darakuneko/Noraneko/noraneko42o/v1.0/firmware/noraneko42o/readme.md

# noraneko42o

noraneko42o

*A short description of the keyboard/project*

* Keyboard Maintainer: [Daraku-Neko](https://github.com/Daraku-Neko)
* Hardware Supported: *The PCBs, controllers supported*
* Hardware Availability: *Links to where you can find this hardware*

Make example for this keyboard (after setting up your build environment):

    make noraneko42o:default

See the [build environment setup](https://docs.qmk.fm/#/getting_started_build_tools) and the [make instructions](https://docs.qmk.fm/#/getting_started_make_guide) for more information. Brand new to QMK? Start with our [Complete Newbs Guide](https://docs.qmk.fm/#/newbs).

## Bootloader

Enter the bootloader in 3 ways:

* **Bootmagic reset**: Hold down the key at (0,0) in the matrix (usually the top left key or Escape) and plug in the keyboard
* **Physical reset button**: Briefly press the button on the back of the PCB - some may have pads you must short instead
* **Keycode in layout**: Press the key mapped to `QK_BOOT` if it is available
