darakuneko/Noraneko/noraneko52r/v1.1/plate/elecrow/noraneko52r-bottom-Thickness3mm.pdf

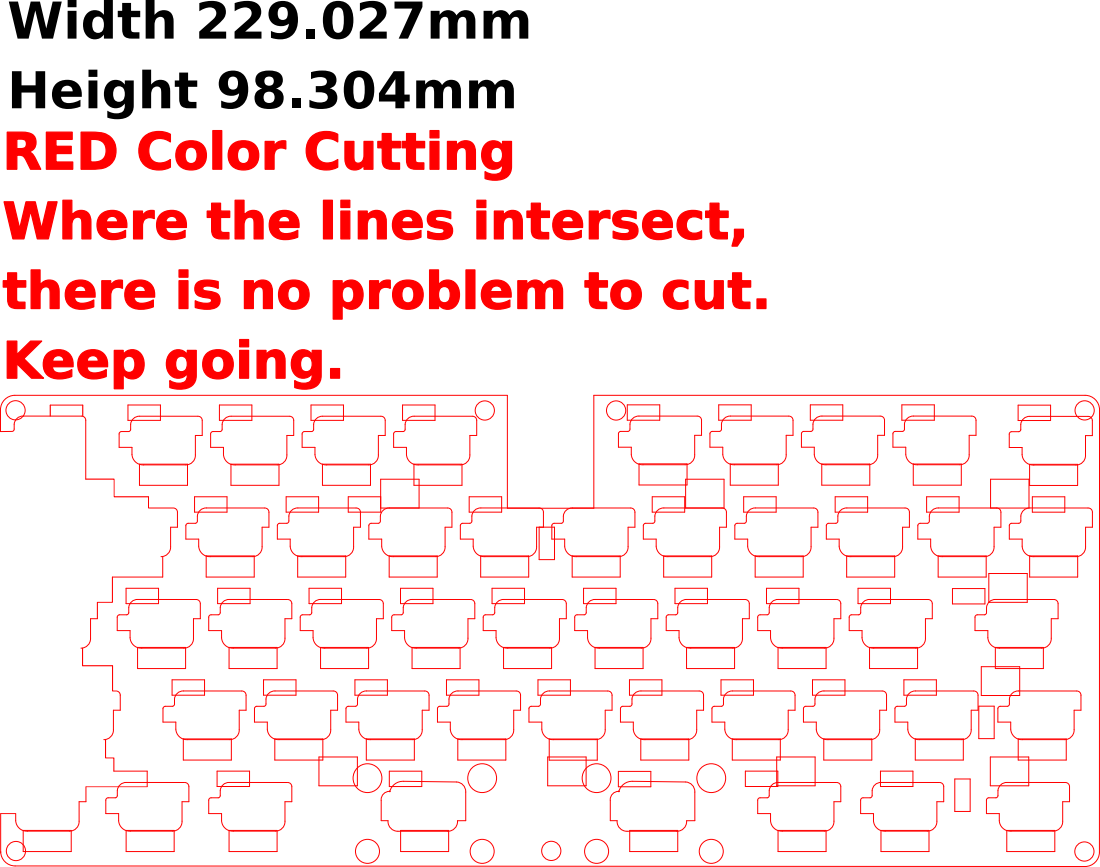
[picture p6: page 1]

Width 229.027mm
Height 98.304mm
RED Color Cutting
Where the lines intersect,
there is no problem to cut.
Keep going.
