darakuneko/Noraneko/noraneko52r/v1.1/plate/elecrow/noraneko52r-bottom-Thickness2mm.pdf

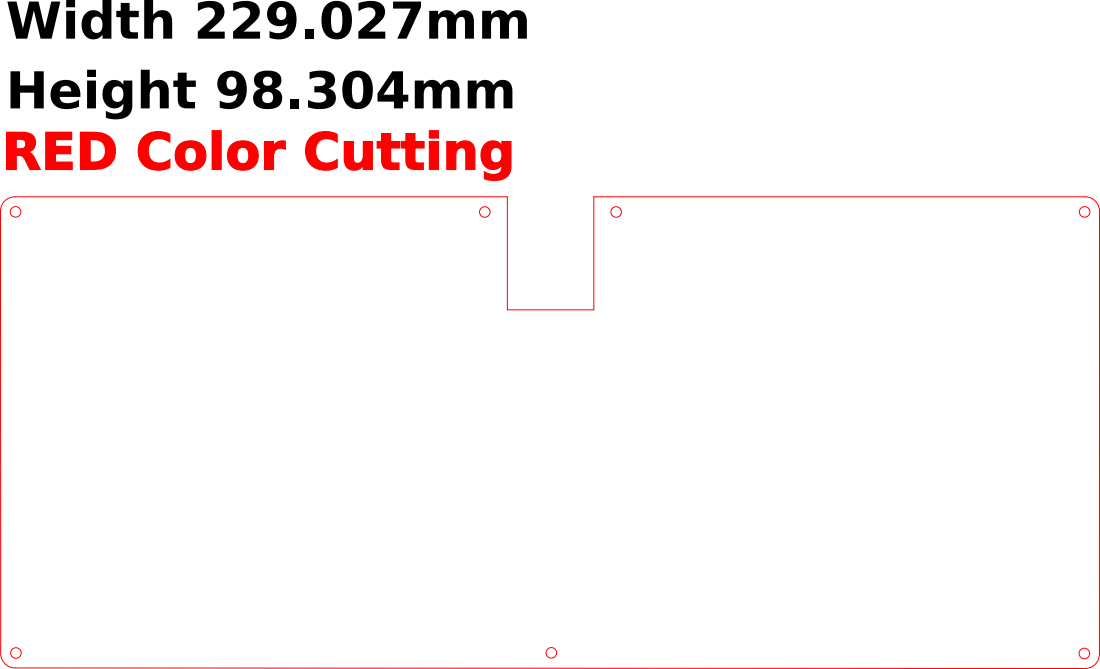
[picture p7: page 1]

Width 229.027mm
Height 98.304mm
RED Color Cutting
