darakuneko/Noraneko/noraneko52r/v1.1/plate/elecrow/noraneko52r-top-Thickness2mm.pdf

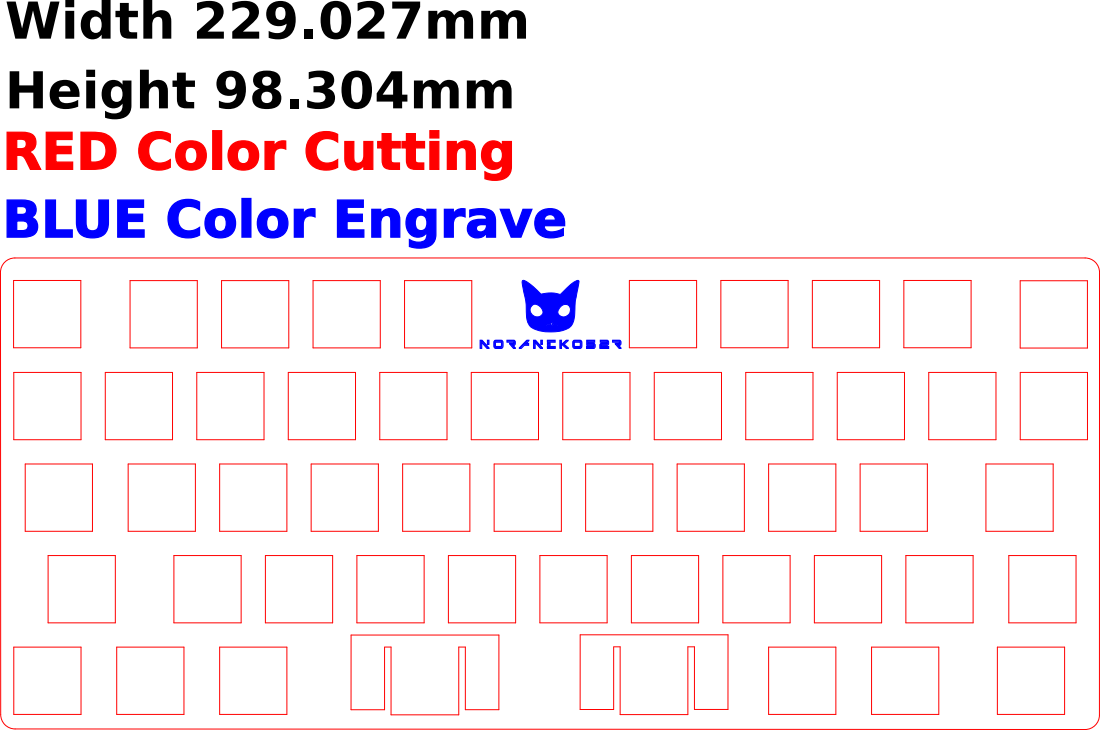
[picture p8: page 1]
Noraneko52R

Width 229.027mm
Height 98.304mm
RED Color Cutting
BLUE Color Engrave
