darakuneko/Noraneko/noraneko42c/v2.0/plate/elecrow/noraneko-top-Thickness3mm.pdf

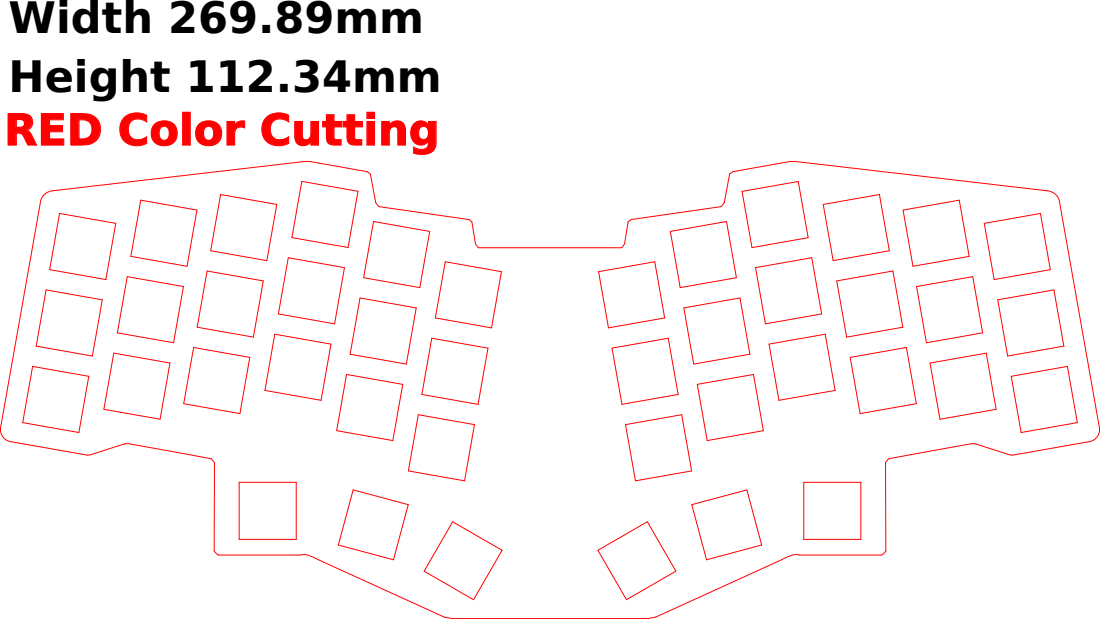
[picture p9: page 1]

Width 269.89mm
Height 112.34mm
RED Color Cutting
