darakuneko/Noraneko/noraneko52r/v1.0/plate/blackout/elecrow/blackout-noraneko52r-top-Thickness2mm.pdf

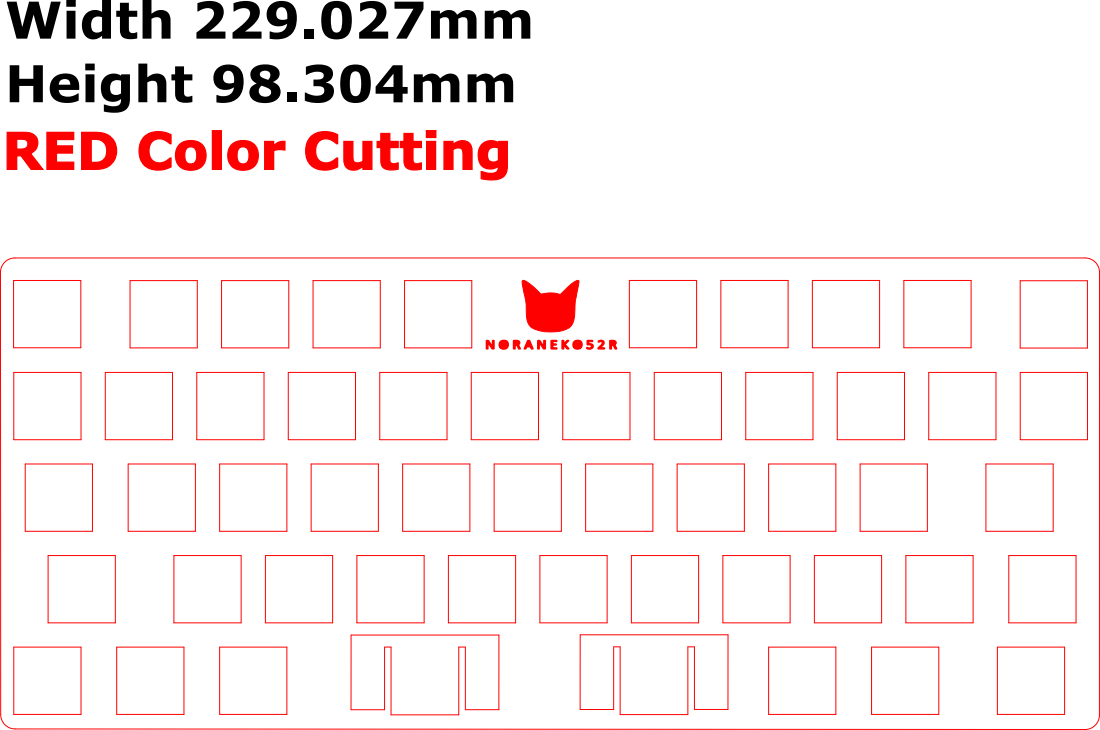
[picture p11: page 1]

Width 229.027mm
Height 98.304mm
RED Color Cutting
