darakuneko/Noraneko/noraneko52r/v1.1/pcb/noraneko52r.kicad_sch

## KiCad design noraneko52r/v1.1/pcb/noraneko52r.kicad_sch (2022-11-11)

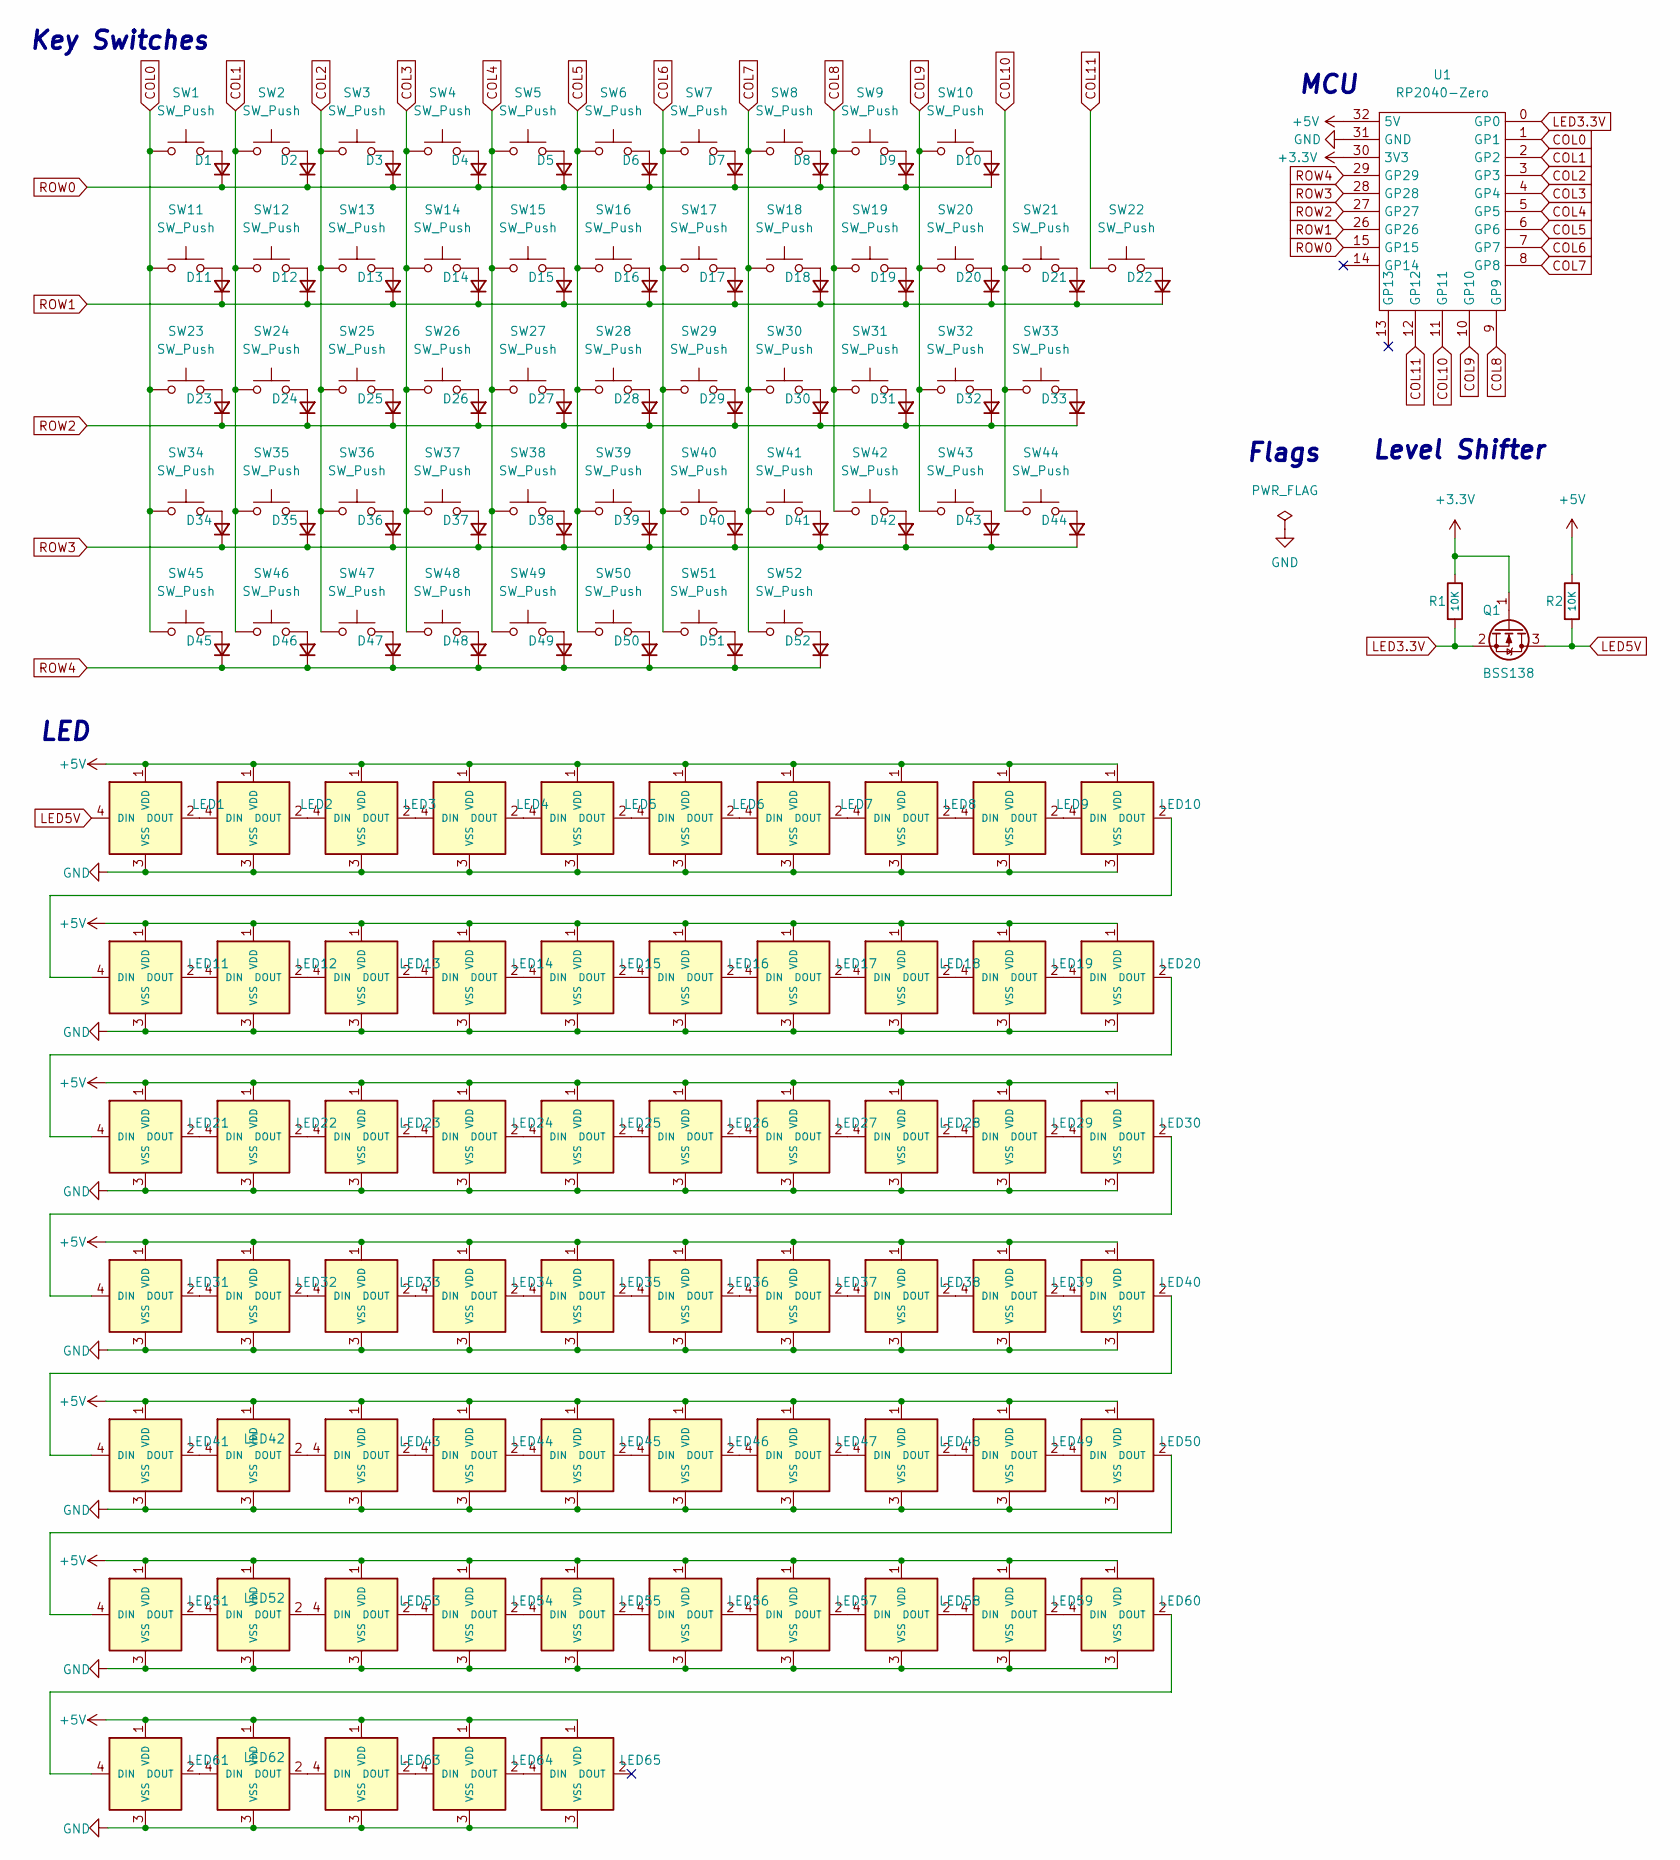
[picture p15: schematic noraneko52r.kicad_sch]

Parts:
D1, D2, D3, D4, D5, D6, D7, D8, D9, D10, D11, D12, D13, D14, D15, D16, D17, D18, D19, D20, D21, D22, D23, D24, D25, D26, D27, D28, D29, D30, D31, D32, D33, D34, D35, D36, D37, D38, D39, D40, D41, D42, D43, D44, D45, D46, D47, D48, D49, D50, D51, D52: D; 1N4148W; LCSC C81598
LED1, LED2, LED3, LED4, LED5, LED6, LED7, LED8, LED9, LED10, LED11, LED12, LED13, LED14, LED15, LED16, LED17, LED18, LED19, LED20, LED21, LED22, LED23, LED24, LED25, LED26, LED27, LED28, LED29, LED30, LED31, LED32, LED33, LED34, LED35, LED36, LED37, LED38, LED39, LED40, LED41, LED42, LED43, LED44, LED45, LED46, LED47, LED48, LED49, LED50, LED51, LED52: SK6812MINI-E
LED53, LED54, LED55, LED56, LED57, LED58, LED59, LED60, LED61, LED62, LED63, LED64, LED65: SK6812MINI-E; LED_WS2812B_PLCC4_5.0x5.0mm_P3.2mm; LCSC C2843785
Q1: BSS138; SOT-23; LCSC C2874697
R1, R2: 10K; R_Axial_DIN0207_L6.3mm_D2.5mm_P7.62mm_Horizontal
SW1, SW2, SW3, SW4, SW5, SW6, SW7, SW8, SW9, SW10, SW11, SW12, SW13, SW14, SW15, SW16, SW17, SW18, SW19, SW20, SW21, SW22, SW24, SW25, SW26, SW27, SW28, SW29, SW30, SW31, SW32, SW35, SW36, SW37, SW38, SW39, SW40, SW41, SW42, SW43, SW45, SW47, SW50: SW_Push; MX_Socket
SW23, SW44, SW46, SW51: SW_Push; MX_Socket_1.25U
SW33, SW34: SW_Push; MX_Socket_1.75U
SW48: SW_Push; MX_Socket_2.75U_Re
SW49: SW_Push; MX_Socket_2.25U_Re
SW52: SW_Push; MX_Socket_1.50U
U1: RP2040-Zero; RP2040-Zero-THT

Connections:
+3.3V: Q1.1 (G), R1.1, U1.30 (3V3)
+5V: LED1.1 (VDD), LED2.1 (VDD), LED3.1 (VDD), LED4.1 (VDD), LED5.1 (VDD), LED6.1 (VDD), LED7.1 (VDD), LED8.1 (VDD), LED9.1 (VDD), LED10.1 (VDD), LED11.1 (VDD), LED12.1 (VDD), LED13.1 (VDD), LED14.1 (VDD), LED15.1 (VDD), LED16.1 (VDD), LED17.1 (VDD), LED18.1 (VDD), LED19.1 (VDD), LED20.1 (VDD), LED21.1 (VDD), LED22.1 (VDD), LED23.1 (VDD), LED24.1 (VDD), LED25.1 (VDD), LED26.1 (VDD), LED27.1 (VDD), LED28.1 (VDD), LED29.1 (VDD), LED30.1 (VDD), LED31.1 (VDD), LED32.1 (VDD), LED33.1 (VDD), LED34.1 (VDD), LED35.1 (VDD), LED36.1 (VDD), LED37.1 (VDD), LED38.1 (VDD), LED39.1 (VDD), LED40.1 (VDD), LED41.1 (VDD), LED42.1 (VDD), LED43.1 (VDD), LED44.1 (VDD), LED45.1 (VDD), LED46.1 (VDD), LED47.1 (VDD), LED48.1 (VDD), LED49.1 (VDD), LED50.1 (VDD), LED51.1 (VDD), LED52.1 (VDD), LED53.1 (VDD), LED54.1 (VDD), LED55.1 (VDD), LED56.1 (VDD), LED57.1 (VDD), LED58.1 (VDD), LED59.1 (VDD), LED60.1 (VDD), LED61.1 (VDD), LED62.1 (VDD), LED63.1 (VDD), LED64.1 (VDD), LED65.1 (VDD), R2.1, U1.32 (5V)
COL0: SW1.1, SW11.1, SW23.1, SW34.1, SW45.1, U1.1 (GP1)
COL1: SW2.1, SW12.1, SW24.1, SW35.1, SW46.1, U1.2 (GP2)
COL2: SW3.1, SW13.1, SW25.1, SW36.1, SW47.1, U1.3 (GP3)
COL3: SW4.1, SW14.1, SW26.1, SW37.1, SW48.1, U1.4 (GP4)
COL4: SW5.1, SW15.1, SW27.1, SW38.1, SW49.1, U1.5 (GP5)
COL5: SW6.1, SW16.1, SW28.1, SW39.1, SW50.1, U1.6 (GP6)
COL6: SW7.1, SW17.1, SW29.1, SW40.1, SW51.1, U1.7 (GP7)
COL7: SW8.1, SW18.1, SW30.1, SW41.1, SW52.1, U1.8 (GP8)
COL8: SW9.1, SW19.1, SW31.1, SW42.1, U1.9 (GP9)
COL9: SW10.1, SW20.1, SW32.1, SW43.1, U1.10 (GP10)
COL10: SW21.1, SW33.1, SW44.1, U1.11 (GP11)
COL11: SW22.1, U1.12 (GP12)
GND: LED1.3 (VSS), LED2.3 (VSS), LED3.3 (VSS), LED4.3 (VSS), LED5.3 (VSS), LED6.3 (VSS), LED7.3 (VSS), LED8.3 (VSS), LED9.3 (VSS), LED10.3 (VSS), LED11.3 (VSS), LED12.3 (VSS), LED13.3 (VSS), LED14.3 (VSS), LED15.3 (VSS), LED16.3 (VSS), LED17.3 (VSS), LED18.3 (VSS), LED19.3 (VSS), LED20.3 (VSS), LED21.3 (VSS), LED22.3 (VSS), LED23.3 (VSS), LED24.3 (VSS), LED25.3 (VSS), LED26.3 (VSS), LED27.3 (VSS), LED28.3 (VSS), LED29.3 (VSS), LED30.3 (VSS), LED31.3 (VSS), LED32.3 (VSS), LED33.3 (VSS), LED34.3 (VSS), LED35.3 (VSS), LED36.3 (VSS), LED37.3 (VSS), LED38.3 (VSS), LED39.3 (VSS), LED40.3 (VSS), LED41.3 (VSS), LED42.3 (VSS), LED43.3 (VSS), LED44.3 (VSS), LED45.3 (VSS), LED46.3 (VSS), LED47.3 (VSS), LED48.3 (VSS), LED49.3 (VSS), LED50.3 (VSS), LED51.3 (VSS), LED52.3 (VSS), LED53.3 (VSS), LED54.3 (VSS), LED55.3 (VSS), LED56.3 (VSS), LED57.3 (VSS), LED58.3 (VSS), LED59.3 (VSS), LED60.3 (VSS), LED61.3 (VSS), LED62.3 (VSS), LED63.3 (VSS), LED64.3 (VSS), LED65.3 (VSS), U1.31 (GND)
LED3.3V: Q1.2 (S), R1.2, U1.0 (GP0)
LED5V: LED1.4 (DIN), Q1.3 (D), R2.2
unnamed: D1.2 (A), SW1.2
unnamed: D2.2 (A), SW2.2
unnamed: D3.2 (A), SW3.2
unnamed: D4.2 (A), SW4.2
unnamed: D5.2 (A), SW5.2
unnamed: D6.2 (A), SW6.2
unnamed: D7.2 (A), SW7.2
unnamed: D8.2 (A), SW8.2
unnamed: D9.2 (A), SW9.2
unnamed: D10.2 (A), SW10.2
unnamed: D11.2 (A), SW11.2
unnamed: D12.2 (A), SW12.2
unnamed: D13.2 (A), SW13.2
unnamed: D14.2 (A), SW14.2
unnamed: D15.2 (A), SW15.2
unnamed: D16.2 (A), SW16.2
unnamed: D17.2 (A), SW17.2
unnamed: D18.2 (A), SW18.2
unnamed: D19.2 (A), SW19.2
unnamed: D20.2 (A), SW20.2
unnamed: D21.2 (A), SW21.2
unnamed: D22.2 (A), SW22.2
unnamed: D23.2 (A), SW23.2
unnamed: D24.2 (A), SW24.2
unnamed: D25.2 (A), SW25.2
unnamed: D26.2 (A), SW26.2
unnamed: D27.2 (A), SW27.2
unnamed: D28.2 (A), SW28.2
unnamed: D29.2 (A), SW29.2
unnamed: D30.2 (A), SW30.2
unnamed: D31.2 (A), SW31.2
unnamed: D32.2 (A), SW32.2
unnamed: D33.2 (A), SW33.2
unnamed: D34.2 (A), SW34.2
unnamed: D35.2 (A), SW35.2
unnamed: D36.2 (A), SW36.2
unnamed: D37.2 (A), SW37.2
unnamed: D38.2 (A), SW38.2
unnamed: D39.2 (A), SW39.2
unnamed: D40.2 (A), SW40.2
unnamed: D41.2 (A), SW41.2
unnamed: D42.2 (A), SW42.2
unnamed: D43.2 (A), SW43.2
unnamed: D44.2 (A), SW44.2
unnamed: D45.2 (A), SW45.2
unnamed: D46.2 (A), SW46.2
unnamed: D47.2 (A), SW47.2
unnamed: D48.2 (A), SW48.2
unnamed: D49.2 (A), SW49.2
unnamed: D50.2 (A), SW50.2
unnamed: D51.2 (A), SW51.2
unnamed: D52.2 (A), SW52.2
unnamed: LED1.2 (DOUT), LED2.4 (DIN)
unnamed: LED2.2 (DOUT), LED3.4 (DIN)
unnamed: LED3.2 (DOUT), LED4.4 (DIN)
unnamed: LED4.2 (DOUT), LED5.4 (DIN)
unnamed: LED5.2 (DOUT), LED6.4 (DIN)
unnamed: LED6.2 (DOUT), LED7.4 (DIN)
unnamed: LED7.2 (DOUT), LED8.4 (DIN)
unnamed: LED8.2 (DOUT), LED9.4 (DIN)
unnamed: LED10.2 (DOUT), LED11.4 (DIN)
unnamed: LED9.2 (DOUT), LED10.4 (DIN)
unnamed: LED11.2 (DOUT), LED12.4 (DIN)
unnamed: LED12.2 (DOUT), LED13.4 (DIN)
unnamed: LED13.2 (DOUT), LED14.4 (DIN)
unnamed: LED14.2 (DOUT), LED15.4 (DIN)
unnamed: LED15.2 (DOUT), LED16.4 (DIN)
unnamed: LED16.2 (DOUT), LED17.4 (DIN)
unnamed: LED17.2 (DOUT), LED18.4 (DIN)
unnamed: LED18.2 (DOUT), LED19.4 (DIN)
unnamed: LED19.2 (DOUT), LED20.4 (DIN)
unnamed: LED20.2 (DOUT), LED21.4 (DIN)
unnamed: LED21.2 (DOUT), LED22.4 (DIN)
unnamed: LED22.2 (DOUT), LED23.4 (DIN)
unnamed: LED23.2 (DOUT), LED24.4 (DIN)
unnamed: LED24.2 (DOUT), LED25.4 (DIN)
unnamed: LED25.2 (DOUT), LED26.4 (DIN)
unnamed: LED26.2 (DOUT), LED27.4 (DIN)
unnamed: LED27.2 (DOUT), LED28.4 (DIN)
unnamed: LED28.2 (DOUT), LED29.4 (DIN)
unnamed: LED29.2 (DOUT), LED30.4 (DIN)
unnamed: LED30.2 (DOUT), LED31.4 (DIN)
unnamed: LED31.2 (DOUT), LED32.4 (DIN)
unnamed: LED32.2 (DOUT), LED33.4 (DIN)
unnamed: LED33.2 (DOUT), LED34.4 (DIN)
unnamed: LED34.2 (DOUT), LED35.4 (DIN)
unnamed: LED35.2 (DOUT), LED36.4 (DIN)
unnamed: LED36.2 (DOUT), LED37.4 (DIN)
unnamed: LED37.2 (DOUT), LED38.4 (DIN)
unnamed: LED38.2 (DOUT), LED39.4 (DIN)
unnamed: LED39.2 (DOUT), LED40.4 (DIN)
unnamed: LED40.2 (DOUT), LED41.4 (DIN)
unnamed: LED41.2 (DOUT), LED42.4 (DIN)
unnamed: LED42.2 (DOUT), LED43.4 (DIN)
unnamed: LED43.2 (DOUT), LED44.4 (DIN)
unnamed: LED44.2 (DOUT), LED45.4 (DIN)
unnamed: LED45.2 (DOUT), LED46.4 (DIN)
unnamed: LED46.2 (DOUT), LED47.4 (DIN)
unnamed: LED47.2 (DOUT), LED48.4 (DIN)
unnamed: LED48.2 (DOUT), LED49.4 (DIN)
unnamed: LED49.2 (DOUT), LED50.4 (DIN)
unnamed: LED50.2 (DOUT), LED51.4 (DIN)
unnamed: LED51.2 (DOUT), LED52.4 (DIN)
unnamed: LED52.2 (DOUT), LED53.4 (DIN)
unnamed: LED53.2 (DOUT), LED54.4 (DIN)
unnamed: LED54.2 (DOUT), LED55.4 (DIN)
unnamed: LED55.2 (DOUT), LED56.4 (DIN)
unnamed: LED56.2 (DOUT), LED57.4 (DIN)
unnamed: LED57.2 (DOUT), LED58.4 (DIN)
unnamed: LED58.2 (DOUT), LED59.4 (DIN)
unnamed: LED59.2 (DOUT), LED60.4 (DIN)
unnamed: LED60.2 (DOUT), LED61.4 (DIN)
unnamed: LED61.2 (DOUT), LED62.4 (DIN)
unnamed: LED62.2 (DOUT), LED63.4 (DIN)
unnamed: LED63.2 (DOUT), LED64.4 (DIN)
unnamed: LED64.2 (DOUT), LED65.4 (DIN)
ROW0: D1.1 (K), D2.1 (K), D3.1 (K), D4.1 (K), D5.1 (K), D6.1 (K), D7.1 (K), D8.1 (K), D9.1 (K), D10.1 (K), U1.15 (GP15)
ROW1: D11.1 (K), D12.1 (K), D13.1 (K), D14.1 (K), D15.1 (K), D16.1 (K), D17.1 (K), D18.1 (K), D19.1 (K), D20.1 (K), D21.1 (K), D22.1 (K), U1.26 (GP26)
ROW2: D23.1 (K), D24.1 (K), D25.1 (K), D26.1 (K), D27.1 (K), D28.1 (K), D29.1 (K), D30.1 (K), D31.1 (K), D32.1 (K), D33.1 (K), U1.27 (GP27)
ROW3: D34.1 (K), D35.1 (K), D36.1 (K), D37.1 (K), D38.1 (K), D39.1 (K), D40.1 (K), D41.1 (K), D42.1 (K), D43.1 (K), D44.1 (K), U1.28 (GP28)
ROW4: D45.1 (K), D46.1 (K), D47.1 (K), D48.1 (K), D49.1 (K), D50.1 (K), D51.1 (K), D52.1 (K), U1.29 (GP29)

Notes on the sheet:
Level Shifter
LED
Flags
MCU
Key Switches
